arminbw/wiretouch/openframeworks/wiretouch_monitor/src/interpolator.cpp

/* WireTouch: an open capacitive multi-touch tracker
 * Copyright (C) 2011-2013 Georg Kaindl and Armin Wagner
 *
 * This file is part of WireTouch
 *
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
 * You should have received a copy of the GNU General Public License
 * along with WireTouch. If not, see <http://www.gnu.org/licenses/>.
 */

#include "interpolator.h"

wtmInterpolator::wtmInterpolator(int sw, int sh, int wf, int hf)
{
    this->sourceWidth           = sw;
    this->sourceHeight          = sh;
    this->widthUpsampling       = wf;
    this->heightUpsampling      = hf;
    this->interpolatedWidth     = (sw-1) * wf;
    this->interpolatedHeight    = (sh-1) * hf;
    this->_fx                   = 1.0 / (2.0 * (double)wf);
    this->_fy                   = 1.0 / (2.0 * (double)hf);
    
    this->interpolatedBuffer    = (double*)malloc(this->interpolatedHeight * this->interpolatedWidth * sizeof(double));
    this->pixels = (unsigned char*)malloc(this->interpolatedHeight * this->interpolatedWidth * sizeof(unsigned char));
}

wtmInterpolator::~wtmInterpolator()
{
    if (this->texture.isAllocated())
        this->texture.clear();
    
    free(this->interpolatedBuffer);
    free(this->pixels);
}

int
wtmInterpolator::getOutputWidth()
{
    return this->interpolatedWidth;
}

int
wtmInterpolator::getOutputHeight()
{
    return this->interpolatedHeight;
}

double
wtmInterpolator::sensorValueAt(int x, int y)
{
    double val = 0.0;
    
    if (NULL != this->values) {
        x = MAX(0, MIN(x, this->sourceWidth-1));
        y = MAX(0, MIN(y, this->sourceHeight-1));
    
        val = (double)this->values[y * this->sourceWidth + x] / 1024.0;
    }
    
    return val;
}

const unsigned char*
wtmInterpolator::currentPixels()
{
    return this->pixels;
}

void
wtmInterpolator::runInterpolation(uint16_t* sensorValues)
{
    this->values = sensorValues;
    this->beginInterpolation();
    
    for (int i=0; i<this->sourceWidth-1; i++) {
        for (int j=0; j<sourceHeight-1; j++) {
            this->beginInterpolate4(i, j);
            
            for (int k=0; k<this->widthUpsampling; k++) {
                for (int l=0; l<this->heightUpsampling; l++) {
                    double val =  this->interpolate4(i, j, k, l, this->_fx * (1.0 + 2*k), this->_fy * (1.0 + 2*l));
                    val = MIN(MAX(0, val), 1.0);
                    
                    this->interpolatedBuffer[((j * this->heightUpsampling + l) * this->interpolatedWidth) + i * this->widthUpsampling + k] = val;
                }
            }
            
            this->finishInterpolate4(i, j);
        }
    }
    
    this->finishInterpolation();
    this->values = NULL;
}

void
wtmInterpolator::beginInterpolation()
{
}

void
wtmInterpolator::finishInterpolation()
{
}

void
wtmInterpolator::beginInterpolate4(int x, int y)
{
}

void
wtmInterpolator::finishInterpolate4(int x, int y)
{
}

double
wtmInterpolator::interpolate4(int x, int y, int ix, int iy, float fx, float fy)
{
    return 0.0;
}

ofTexture*
wtmInterpolator::currentTexture()
{
    int i, num_pixels = this->interpolatedWidth * this->interpolatedHeight;
    
    if (!this->texture.isAllocated()) {
        this->texture.allocate(this->interpolatedWidth, this->interpolatedHeight, GL_LUMINANCE);
        this->texture.setTextureMinMagFilter(GL_NEAREST, GL_NEAREST);
    }
    
    for (i=0; i<num_pixels; i++) {
        this->pixels[i] = (unsigned char)(255 - this->interpolatedBuffer[i] * 255);
    }
    
    this->texture.loadData(this->pixels, this->interpolatedWidth, this->interpolatedHeight, GL_LUMINANCE);
    
    return &this->texture;
}
