arminbw/wiretouch/openframeworks/wiretouch_monitor/src/wtmApp_Gui.cpp

/* WireTouch: an open capacitive multi-touch tracker
 * Copyright (C) 2011-2013 Georg Kaindl and Armin Wagner
 *
 * This file is part of WireTouch
 *
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
 * You should have received a copy of the GNU General Public License
 * along with WireTouch. If not, see <http://www.gnu.org/licenses/>.
 */

#include "wtmApp.h"
#include "cJSON.h"

//--------------------------------------------------------------
void wtmApp::initGUI() {
    // setup the graphical user interface
    gui = new ofxUISuperCanvas(WIRETOUCHVERSION, WINDOWWIDTH-(GUIWIDTH+WINDOWBORDERDISTANCE), WINDOWBORDERDISTANCE, GUIWIDTH, GUIHEIGHT);
    gui->addSpacer();
    
    gui->addWidgetDown(new ofxUILabel("SENSOR PARAMETERS", OFX_UI_FONT_MEDIUM));
    gui->addSlider(kGUIHalfwaveAmpName, 1.0, 255.0, 164, WIDGETWIDTH, WIDGETHEIGHT)->setLabelPrecision(0);
    gui->addSlider(kGUIOutputAmpName, 1.0, 255.0, 111, WIDGETWIDTH, WIDGETHEIGHT)->setLabelPrecision(0);
    gui->addSlider(kGUISampleDelayName, 1.0, 100.0, 1, WIDGETWIDTH, WIDGETHEIGHT)->setLabelPrecision(0);
    ofxUISlider* slider = gui->addSlider(kGUISignalFrequencyName, 60.0, 10.0, 20, WIDGETWIDTH, WIDGETHEIGHT);
    slider->setLabelPrecision(2);
    this->updateFrequencyLabel();
    gui->addSpacer();
    
    gui->addWidgetDown(new ofxUILabel("INTERPOLATION", OFX_UI_FONT_MEDIUM));
    vector<string> interpolationTypes;
    interpolationTypes.push_back(kGUILinearName);
    interpolationTypes.push_back(kGUICatmullName);
    interpolationTypes.push_back(kGUICosineName);
    interpolationTypes.push_back(kGUICubicName);
    interpolationTypes.push_back(kGUIHermiteName);
    interpolationTypes.push_back(kGUIWNNName);
    interpolationTypes.push_back(kGUILagrangeName);
    ofxUIDropDownList *interpolationDropDownMenu = gui->addDropDownList(kGUIInterpolationDropDownName, interpolationTypes, WIDGETWIDTH);
    interpolationDropDownMenu->setAutoClose(true);
    interpolationDropDownMenu->getSelected().push_back(gui->getWidget(kGUICatmullName));
    interpolationDropDownMenu->setShowCurrentSelected(true);
    gui->addSlider(kGUIUpSamplingName, 1.0, 12.0, 8, WIDGETWIDTH, WIDGETHEIGHT)->setLabelPrecision(0);
    gui->addSpacer();
    
    gui->addWidgetDown(new ofxUILabel("BLOB DETECTION", OFX_UI_FONT_MEDIUM));
    gui->addSlider(kGUIBlobGammaName, 0.0, 16.0, this->inputGamma, WIDGETWIDTH, WIDGETHEIGHT)->setLabelPrecision(2);
    gui->addSlider(kGUIBlobThresholdName, 0.0, 255.0, 161, WIDGETWIDTH, WIDGETHEIGHT)->setLabelPrecision(0);
    this->blobTracker->setThreshold(161);
    gui->addSlider(kGUIBlobVisualizationName, 0.0, 255.0, 31, WIDGETWIDTH, WIDGETHEIGHT)->setLabelPrecision(0);
    gui->addSlider(kGUIBlobAdaptiveThresholdRangeName, 3.0, 100.0, 41, WIDGETWIDTH, WIDGETHEIGHT);
    this->blobTracker->setAdaptiveThresholdRange(((int) 41) | 1);
    ofxUILabelToggle* toggle = gui->addLabelToggle(kGUIBlobsName, false, WIDGETWIDTH, WIDGETHEIGHT);
    gui->addSpacer();
    
    gui->addWidgetDown(new ofxUILabel("CALIBRATION", OFX_UI_FONT_MEDIUM));
    gui->addLabelButton(kGUICalibrateName, false, WIDGETWIDTH, WIDGETHEIGHT);
    gui->addLabelButton(kGUIResetName, false, WIDGETWIDTH, WIDGETHEIGHT);
    gui->addSpacer();

    gui->addWidgetDown(new ofxUILabel("CONNECTION", OFX_UI_FONT_MEDIUM));
	vector <ofSerialDeviceInfo> deviceList = serial.getDeviceList();
    for(int i=0; i<deviceList.size(); i++) {
        this->serialDevicesNames.push_back(deviceList[i].getDeviceName().c_str());
    }
    ofxUIDropDownList *serialDeviceDropDownMenu = gui->addDropDownList(kGUISerialDropDownName, serialDevicesNames, WIDGETWIDTH);
    serialDeviceDropDownMenu->setShowCurrentSelected(true);
    serialDeviceDropDownMenu->setAutoClose(true);
    
    gui->addLabelButton(kGUIStartName, false, WIDGETWIDTH, WIDGETHEIGHT);
    gui->addSpacer();

    ofxUILabel* firmwareLabel = new ofxUILabel(kGUIFirmwareName, OFX_UI_FONT_SMALL);
    gui->addWidgetDown(firmwareLabel);
    this->updateFirmwareVersionLabel("unknown");

    ofxUILabel* fpsLabel = new ofxUILabel(kGUIFPS, OFX_UI_FONT_SMALL);
    gui->addWidgetDown(fpsLabel);
    this->updateFPSLabelWithValue(0.);
    
    gui->setWidgetColor(OFX_UI_WIDGET_COLOR_BACK, ofColor(51, 51, 51));                       // slider background, button color
    gui->setWidgetColor(OFX_UI_WIDGET_COLOR_OUTLINE_HIGHLIGHT, ofColor(41, 41, 41));
    gui->setWidgetColor(OFX_UI_WIDGET_COLOR_FILL, ofColor(255, 255, 255, 140));               // font color
    gui->setWidgetColor(OFX_UI_WIDGET_COLOR_FILL_HIGHLIGHT, ofColor(82, 208, 207));           // pressed button
    gui->setColorBack(ofColor(51, 51, 52, 140));
    ofAddListener(gui->newGUIEvent, this, &wtmApp::guiEvent);
}

//--------------------------------------------------------------
void wtmApp::saveSettings() {
    ofLogNotice() << "saving settings";
    cJSON *root = cJSON_CreateObject();
    const char* sliderNames[9] = {
        kGUIHalfwaveAmpName, kGUIOutputAmpName, kGUISampleDelayName, kGUISignalFrequencyName, kGUIUpSamplingName,
        kGUIBlobThresholdName, kGUIBlobVisualizationName, kGUIBlobGammaName, kGUIBlobAdaptiveThresholdRangeName
    };
    for (int i=0; i < 8; i++) {
        cJSON_AddNumberToObject(root, sliderNames[i], ((ofxUISlider *) gui->getWidget(sliderNames[i]))->getValue() );
    }
    
    ofxUIDropDownList *interpolationDropDown = (ofxUIDropDownList *) gui->getWidget(kGUIInterpolationDropDownName);
    if (!(vector<string> *) interpolationDropDown->getSelectedNames().empty())
        cJSON_AddStringToObject(root, kGUIInterpolationDropDownName, interpolationDropDown->getSelectedNames()[0].c_str() );
    ofxUIDropDownList *serialDropDown = (ofxUIDropDownList *) gui->getWidget(kGUISerialDropDownName);
    if (!(vector<string> *) serialDropDown->getSelectedNames().empty())
        cJSON_AddStringToObject(root, kGUISerialDropDownName, serialDropDown->getSelectedNames()[0].c_str() );
    
    cJSON_AddNumberToObject(root, kGUIBlobsName, (int) this->bTrackBlobs );
    
    char *renderedJson = cJSON_Print(root);
    ofFile file;
    file.open(ofToDataPath("settings.json"), ofFile::WriteOnly, false);
    file << renderedJson;
    file.close();
    cJSON_Delete(root);
    delete(renderedJson);
}

//--------------------------------------------------------------
void wtmApp::loadSettings() {
    ofLogNotice() << "loading settings";
    ofFile file;
    if (!file.doesFileExist(ofToDataPath("settings.json"))) {
        ofLogError() << "no settings file found";
        return;
    }
    file.open(ofToDataPath("settings.json"), ofFile::ReadOnly, false);
    ofBuffer buffer = file.readToBuffer();
    cJSON *root = cJSON_Parse((buffer.getText()).c_str());
    
    const char* sliderNames[9] = {
        kGUIHalfwaveAmpName, kGUIOutputAmpName, kGUISampleDelayName, kGUISignalFrequencyName, kGUIUpSamplingName,
        kGUIBlobThresholdName, kGUIBlobVisualizationName, kGUIBlobGammaName, kGUIBlobAdaptiveThresholdRangeName
    };
    for (int i=0; i < 8; i++) {
        if (cJSON_GetObjectItem(root, sliderNames[i]) != NULL) {
            ((ofxUISlider *) gui->getWidget(sliderNames[i]))->setValue(cJSON_GetObjectItem(root, sliderNames[i])->valueint);
        }
    }
    this->updateFrequencyLabel();
    this->updateInterpolator();
    
    if (cJSON_GetObjectItem(root, kGUIInterpolationDropDownName) != NULL)
        gui->triggerEvent(gui->getWidget(cJSON_GetObjectItem(root, kGUIInterpolationDropDownName)->valuestring));
    if (cJSON_GetObjectItem(root, kGUISerialDropDownName) != NULL) {
        string selectedDeviceName = (char *) cJSON_GetObjectItem(root, kGUISerialDropDownName)->valuestring;
        ofxUIDropDownList *serialDropDown = (ofxUIDropDownList *) gui->getWidget(kGUISerialDropDownName);
        for (int i=0; i<this->serialDevicesNames.size(); ++i) {
            if (selectedDeviceName == serialDevicesNames[i]) {
                moveWidgetsBeneathDropdown(serialDropDown, false); // TODO: refactor
                serialDropDown->triggerEvent(gui->getWidget(cJSON_GetObjectItem(root, kGUISerialDropDownName)->valuestring));
            }
        }
    }
    if (cJSON_GetObjectItem(root, kGUIBlobsName) != NULL) {
        this->bTrackBlobs = (bool) cJSON_GetObjectItem(root, kGUIBlobsName)->valueint;
        ((ofxUILabelToggle *) gui->getWidget(kGUIBlobsName))->setValue(this->bTrackBlobs);
    }
    file.close();
    cJSON_Delete(root);
}

//--------------------------------------------------------------
void wtmApp::updateFPSLabelWithValue(float fps) {
    ofxUILabel* fpsLabel = (ofxUILabel*) gui->getWidget(kGUIFPS);
    if (NULL != fpsLabel) {
        char buf[16];
        snprintf(buf, 16, "FPS: %.2f", fps);
        fpsLabel->setLabel(buf);
    }
}

//--------------------------------------------------------------
void wtmApp::updateFirmwareVersionLabel(const char* newVersion) {
    ofxUILabel* firmwareLabel = (ofxUILabel*)gui->getWidget(kGUIFirmwareName);
    if (NULL != firmwareLabel) {
        char buf[64];
        snprintf(buf, 64, "FIRMWARE VERSION: %s", newVersion);
        
        firmwareLabel->setLabel(buf);
    }
}

//--------------------------------------------------------------
void wtmApp::updateFrequencyLabel() {
    ofxUISlider* slider = (ofxUISlider*) gui->getWidget(kGUISignalFrequencyName);
    int reverseValue = (round(slider->getValue()));
    slider->getLabelWidget()->setLabel(slider->getName() + ": ~" + ofxUIToString(16000000./(round(reverseValue)+0.5)/2000., 0) + " kHz");
}

//--------------------------------------------------------------
// The current implementation of ofxUIDropDownList is problematic
// as it triggers events of widgets positioned underneath the dropdown menu.
// This workaround changes the dropdown menu into a "disclosure menu".
//
void wtmApp::moveWidgetsBeneathDropdown(ofxUIDropDownList* widget, bool moveBack) {
    // calculate the size of the toggles
    float summand = 0;
    vector<ofxUILabelToggle*> toggles = widget->getToggles();
    for (vector<ofxUILabelToggle*>::iterator it = toggles.begin(); it != toggles.end(); ++it) {
        ofxUIRectangle* r = (*it)->getRect();
        summand += r->getHeight();
    }
    if (moveBack) summand = -summand;
    // now change the position of every widget beneath
    vector<ofxUIWidget*> widgets = gui->getWidgets();
    for (vector<ofxUIWidget*>::reverse_iterator rit = widgets.rbegin(); rit != widgets.rend(); ++rit) {
        if (*rit == widget) break; // everything above the widget won't get changed
        if ((*rit)->getParent() == gui) { // only top-level widgets get changed
            ofxUIRectangle* r = (*rit)->getRect();
            r->setY(r->getY(false)+summand);
        }
    }
    gui->setHeight(gui->getRect()->getHeight()+summand);
}

//--------------------------------------------------------------
void wtmApp::guiEvent(ofxUIEventArgs &e) {
    string widgetName = e.widget->getName();
    // ofLogNotice() << "widget activated: " << widgetName;

    // interpolation type disclosure menu
    ofxUIDropDownList *dropDownlist = (ofxUIDropDownList *) gui->getWidget(kGUIInterpolationDropDownName);
    if (widgetName == kGUIInterpolationDropDownName) {
        moveWidgetsBeneathDropdown(dropDownlist, !dropDownlist->isOpen());
        return;
    }
    if (e.widget->getParent() == dropDownlist) {
        if (widgetName == kGUILinearName) this->interpolatorType = wtmInterpolatorTypeLinear;
        if (widgetName == kGUICatmullName) this->interpolatorType = wtmInterpolatorTypeCatmullRom;
        if (widgetName == kGUICosineName) this->interpolatorType = wtmInterpolatorTypeCosine;
        if (widgetName == kGUICubicName) this->interpolatorType = wtmInterpolatorTypeCubic;
        if (widgetName == kGUIHermiteName) this->interpolatorType = wtmInterpolatorTypeHermite;
        if (widgetName == kGUIWNNName) this->interpolatorType = wtmInterpolatorTypeWNN;
        if (widgetName == kGUILagrangeName) this->interpolatorType = wtmInterpolatorTypeLagrange;
        this->updateInterpolator();
        dropDownlist->setLabelText(widgetName.c_str());
        return;
    }
    
    // serial connection disclosure menu
    dropDownlist = (ofxUIDropDownList *) gui->getWidget(kGUISerialDropDownName);
    if (widgetName == kGUISerialDropDownName) {
        moveWidgetsBeneathDropdown(dropDownlist, !dropDownlist->isOpen());
        return;
    }
    if (e.widget->getParent() == dropDownlist) {
        if (serial.isInitialized()) {
            ofLogNotice() << "serial connection changed";
            if (this->state == wtmAppStateReceivingTouches) {
                stopSensor();
                ofxUILabelButton *startButton = (ofxUILabelButton *) gui->getWidget(kGUIStartName);
            }
            closeSerialConnection();
        }
        return;
    }
    
    // push buttons
    if (e.widget->getKind() == OFX_UI_WIDGET_LABELBUTTON) {
        ofxUILabelButton *button = (ofxUILabelButton *) e.widget;
        if (button->getValue() == 1) { // we only use button-released, not button-pressed and not both
            if (widgetName == kGUIStartName) {
                if (wtmAppStateNoSerialConnection == this->state) {
                    vector<string> selected = dropDownlist->getSelectedNames();
                    if (selected.empty()) {
                        ofLogError() << "no serial connection selected";
                    } else {
                        initAndStartSerialConnection(selected[0]);
                        button->setLabelText(kGUIStopName);
                    }
                    return;
                }
                if (wtmAppStateIdle == this->state) {
                    this->startSensor();
                    button->setLabelText(kGUIStopName);
                    return;
                }
                if (wtmAppStateReceivingTouches == this->state) {
                    this->stopSensor();
                    button->setLabelText(kGUIStartName);
                    return;
                }
                return;
            }
            if (widgetName == kGUICalibrateName) {
                if (wtmAppStateReceivingTouches == this->state) {
                    this->stopSensor(); // TODO: serial buffer issue
                    ofSleepMillis(100); // this is a
                    this->stopSensor(); // lousy workaround
                    this->startCalibration();
                    button->setLabelText("CALIBRATING...");
                }
                return;
            }
            if (widgetName == kGUIResetName) {
                if (wtmAppStateReceivingTouches == this->state) {
                    this->resetCalibration();
                }
            }
        }
    }
    
    // toggle buttons
    if (e.widget->getKind() == OFX_UI_WIDGET_LABELTOGGLE) {
        ofxUILabelToggle *toggle = (ofxUILabelToggle *) e.widget;
        if (widgetName == kGUIBlobsName) {
            bTrackBlobs = toggle->getValue();
            return;
        }
    }
    
    // sliders
    if (e.widget->getKind() == OFX_UI_WIDGET_SLIDER_H) {
        ofxUISlider *slider = (ofxUISlider *) e.widget;
        float val = slider->getValue();
        if (widgetName == kGUIHalfwaveAmpName) {
            slider->setValue(round(val));
            sendSliderData(slider);
        } else if (widgetName == kGUIOutputAmpName) {
            slider->setValue(round(val));
            sendSliderData(slider);
        } else if (widgetName == kGUISampleDelayName) {
            slider->setValue(round(val));
            sendSliderData(slider);
        } else if (widgetName == kGUIUpSamplingName) {
            int oldValue = this->interpolatorUpsampleX;
            int newValue = round(val);
            slider->setValue(newValue);
            if (oldValue != newValue) {
                this->interpolatorUpsampleX = newValue;
                this->interpolatorUpsampleY = newValue;
                this->updateInterpolator();
            }
        } else if (widgetName == kGUISignalFrequencyName) {
            slider->setValue(round(val));
            this->updateFrequencyLabel();
            sendSliderData(slider);
        } else if (widgetName == kGUIBlobThresholdName) {
            slider->setValue(round(val));
            this->blobTracker->setThreshold(round(val));
        } else if (widgetName == kGUIBlobVisualizationName) {
            slider->setValue(round(val));
            this->thresholdImageAlpha = round(val);
        } else if (widgetName == kGUIBlobAdaptiveThresholdRangeName) {
            double value = (slider->getValue()/100.0) * this->interpolator->getOutputWidth();
            this->blobTracker->setAdaptiveThresholdRange(((int) value) | 1);
        } else if (widgetName == kGUIBlobGammaName) {
            this->inputGamma = slider->getValue();
        }
    }
}

//--------------------------------------------------------------
void wtmApp::keyReleased(int key) {
    if (key == 'y') {
        this->changeMeasurement();
    }
}

//--------------------------------------------------------------
void wtmApp::keyPressed(int key) {
    
}

//--------------------------------------------------------------
void wtmApp::mouseMoved(int x, int y ) {
    
}

//--------------------------------------------------------------
void wtmApp::mouseDragged(int x, int y, int button) {
    
}

//--------------------------------------------------------------
void wtmApp::mousePressed(int x, int y, int button) {
    
}

//--------------------------------------------------------------
void wtmApp::mouseReleased(int x, int y, int button) {
    // the gui title bar shouldn't leave the app window
    if (gui->getRect()->getY() < 0) {
        gui->getRect()->setY((0.0));
    }
}

//--------------------------------------------------------------
void wtmApp::windowResized(int w, int h) {
    this->lastWindowResizeTime = ofGetElapsedTimef();
}

//--------------------------------------------------------------
void wtmApp::gotMessage(ofMessage msg) {
    
}

//--------------------------------------------------------------
void wtmApp::dragEvent(ofDragInfo dragInfo) {
    
}
